mariamihalcea/ebook_reader-TSC/Images/display.png

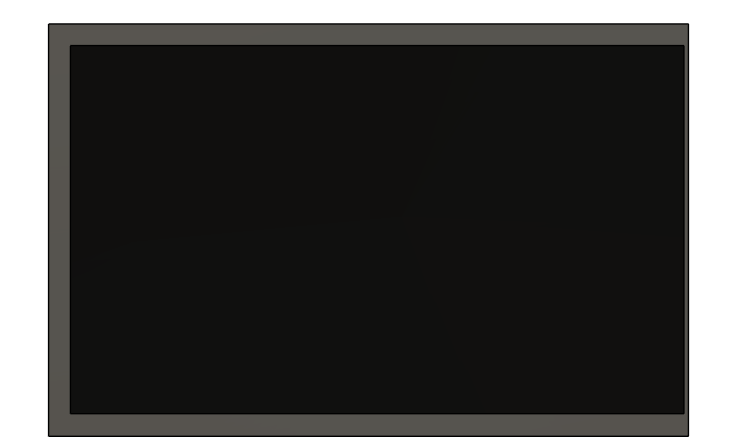
Images/display.png
